DitroniX/IPEM-PiHat-IoT-Power-Energy-Monitor/Datasheets and Information/DitroniX.net Raspberry Pi 5 - Heatsink and Fan.jpg

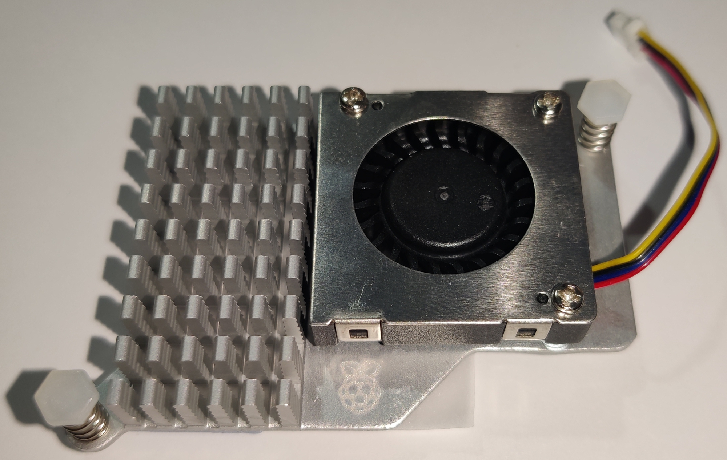
Datasheets and Information/DitroniX.net Raspberry Pi 5 - Heatsink and Fan.jpg
