DitroniX/IPEM-PiHat-IoT-Power-Energy-Monitor/Datasheets and Information/DitroniX.net Raspberry Pi 5 - IPEM Power Energy Monitor Border.jpg

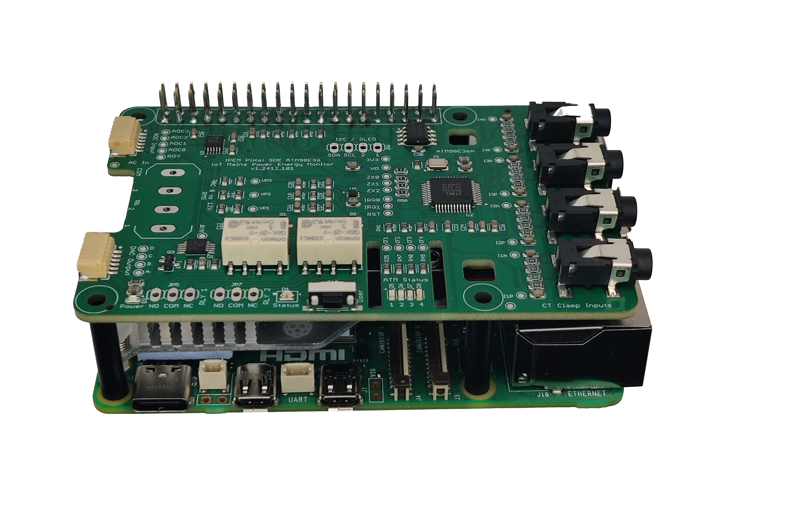
Datasheets and Information/DitroniX.net Raspberry Pi 5 - IPEM Power Energy Monitor Border.jpg
