DitroniX/IPEM-PiHat-IoT-Power-Energy-Monitor/Datasheets and Information/DitroniX.net Raspberry Pi 5 -Fan Socket.jpg

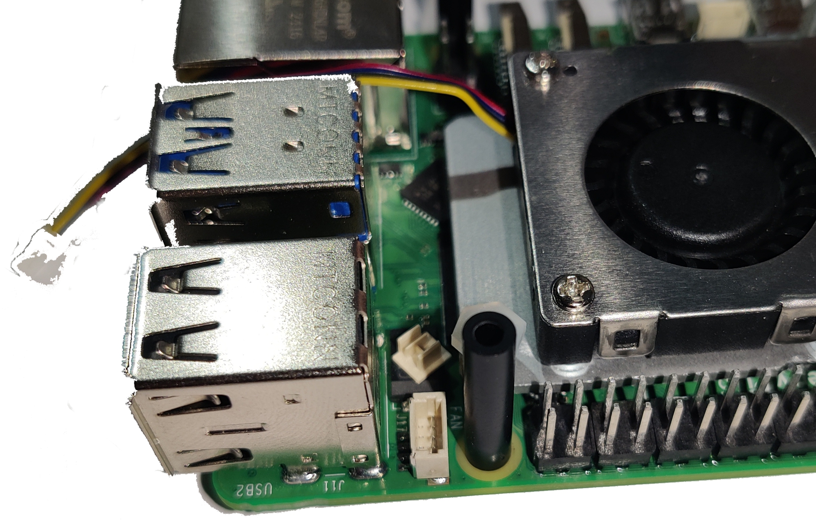
Datasheets and Information/DitroniX.net Raspberry Pi 5 -Fan Socket.jpg
