DitroniX/IPEM-PiHat-IoT-Power-Energy-Monitor/Datasheets and Information/IPEM PiHat 1.2502.102 PreProd BTM.jpg

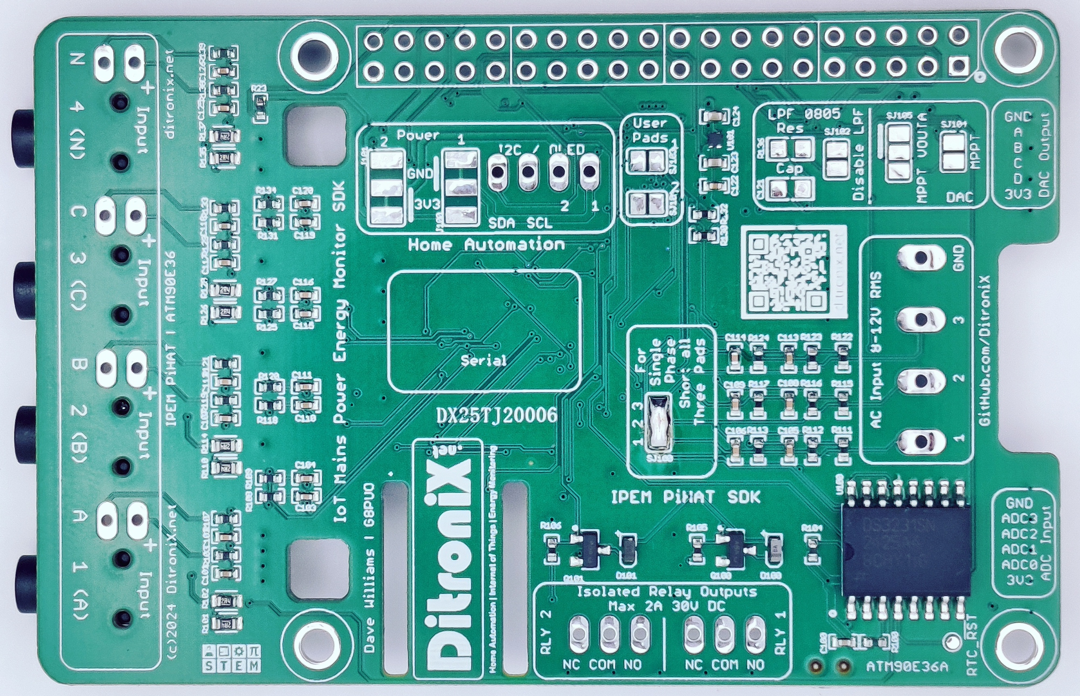
Datasheets and Information/IPEM PiHat 1.2502.102 PreProd BTM.jpg
