DitroniX/IPEM-PiHat-IoT-Power-Energy-Monitor/Datasheets and Information/IPEM PiHat - Single Phase Jumpers.png

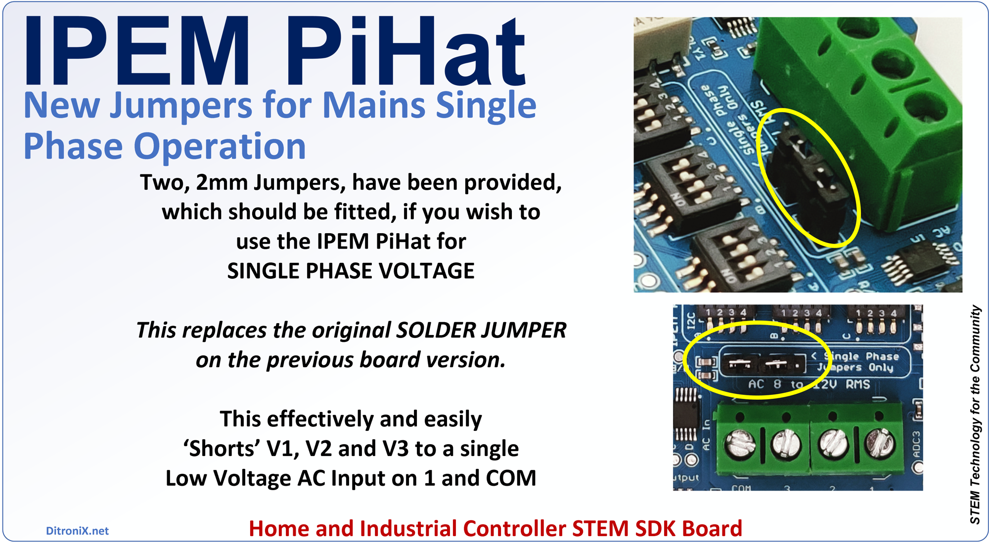
Datasheets and Information/IPEM PiHat - Single Phase Jumpers.png
