DitroniX/IPEM-PiHat-IoT-Power-Energy-Monitor/Datasheets and Information/IPEM PiHat Accessories.jpg

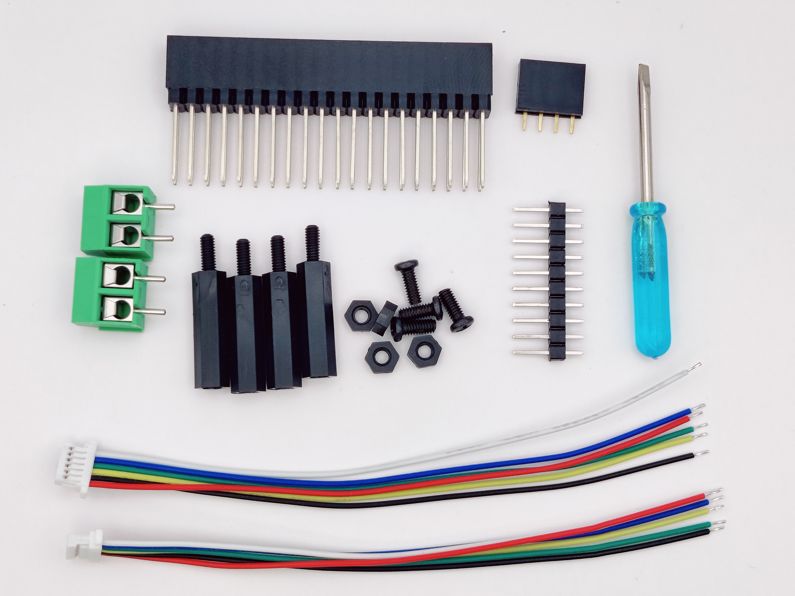
Datasheets and Information/IPEM PiHat Accessories.jpg
