DitroniX/IPEM-PiHat-IoT-Power-Energy-Monitor/Datasheets and Information/IPEM PiHat ATM90E32 ATM90E36 Beta Preview.png

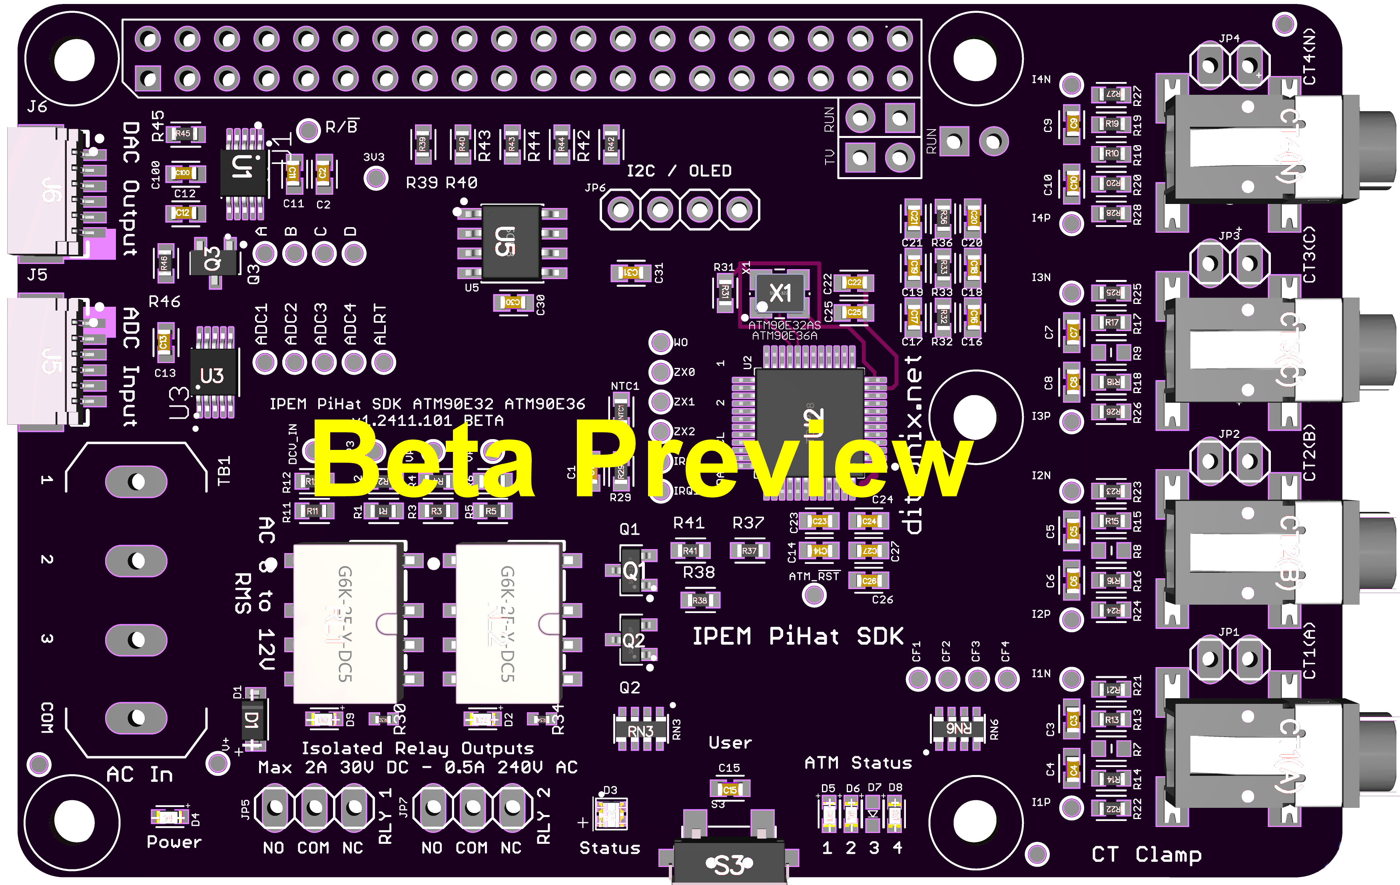
Datasheets and Information/IPEM PiHat ATM90E32 ATM90E36 Beta Preview.png
