DitroniX/IPEM-PiHat-IoT-Power-Energy-Monitor/Datasheets and Information/IPEM PiHat Comparison Chart.jpg

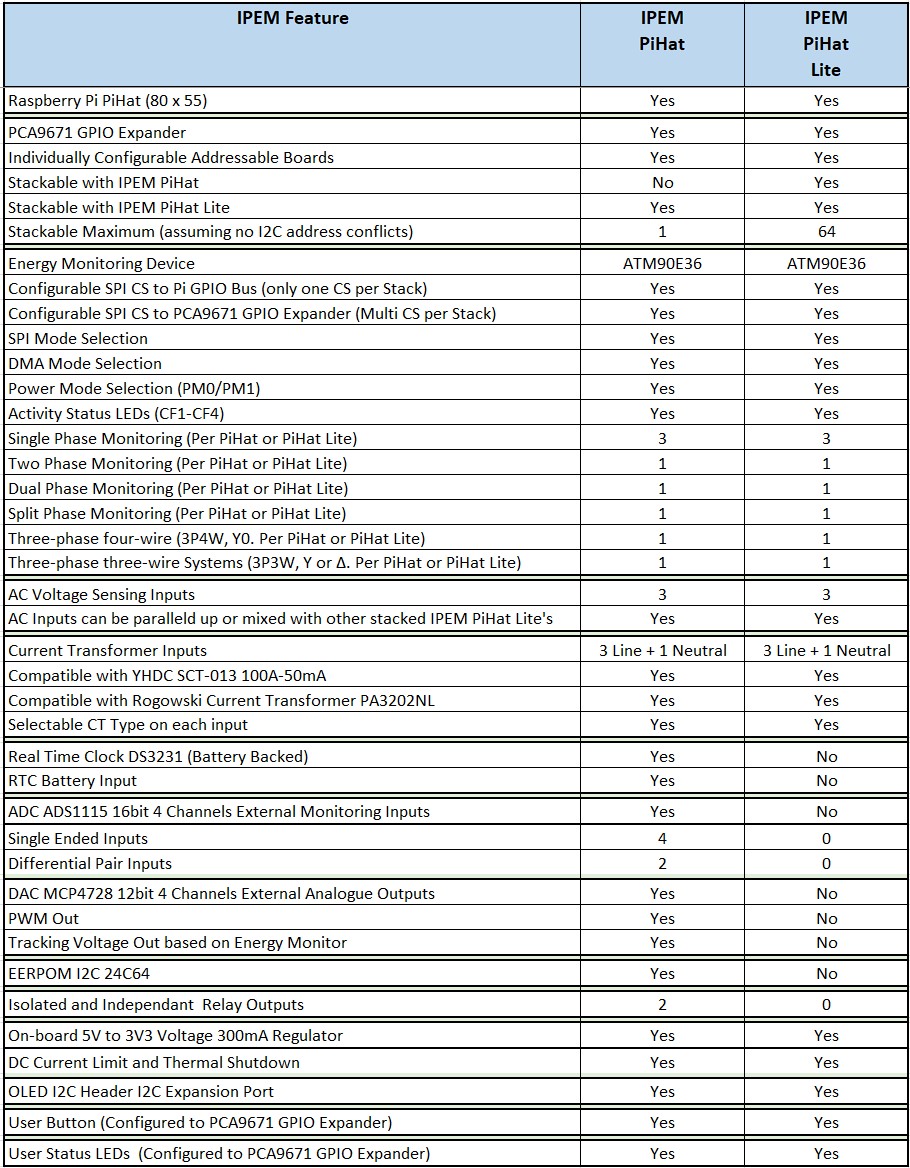
Datasheets and Information/IPEM PiHat Comparison Chart.jpg
