DitroniX/IPEM-PiHat-IoT-Power-Energy-Monitor/Datasheets and Information/IPEM PiHat Header GPIOs.jpg

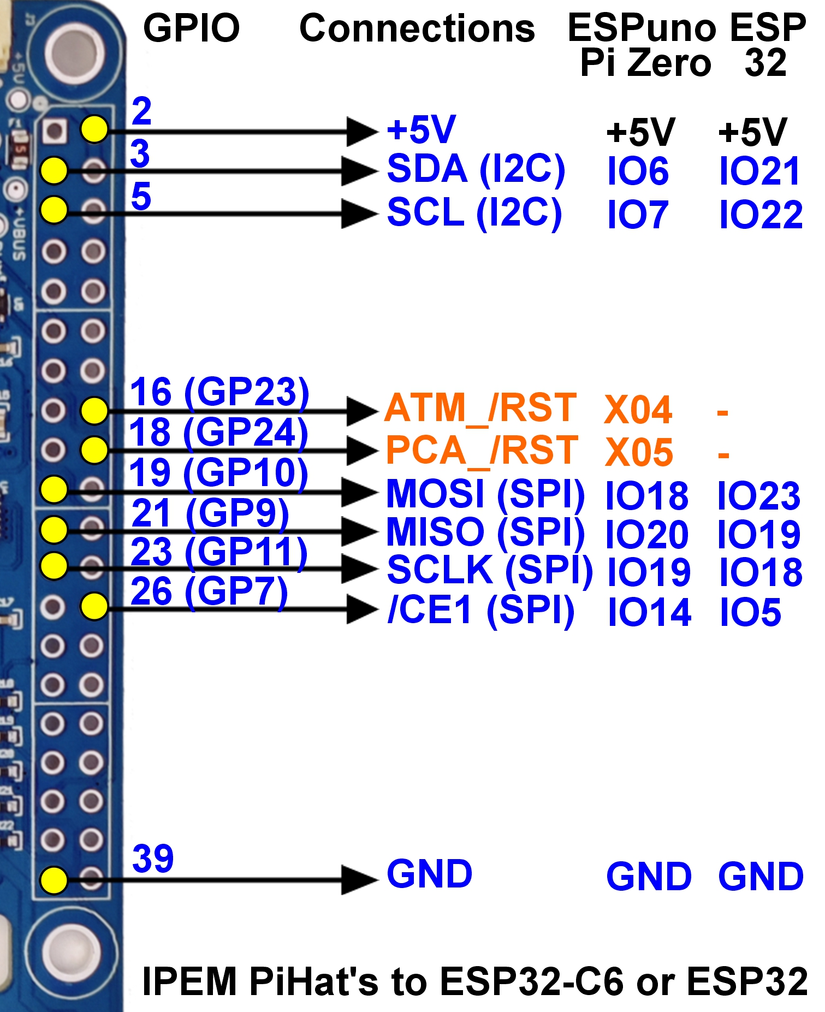
Datasheets and Information/IPEM PiHat Header GPIOs.jpg
