DitroniX/IPEM-PiHat-IoT-Power-Energy-Monitor/Datasheets and Information/IPEM PiHat Isolated Relays.jpg

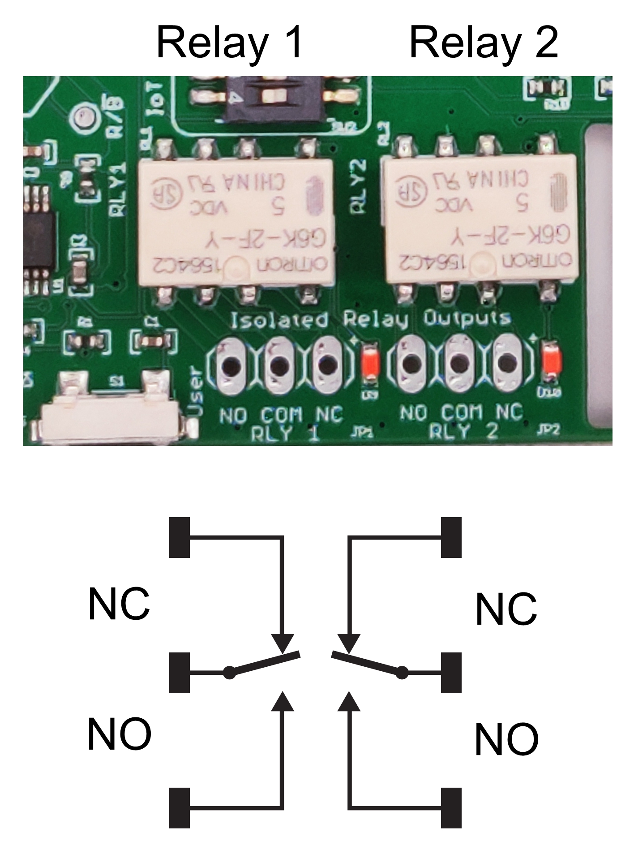
Datasheets and Information/IPEM PiHat Isolated Relays.jpg
