DitroniX/IPEM-PiHat-IoT-Power-Energy-Monitor/Datasheets and Information/IPEM PiHat Layout Topology - DIP Switches.jpg

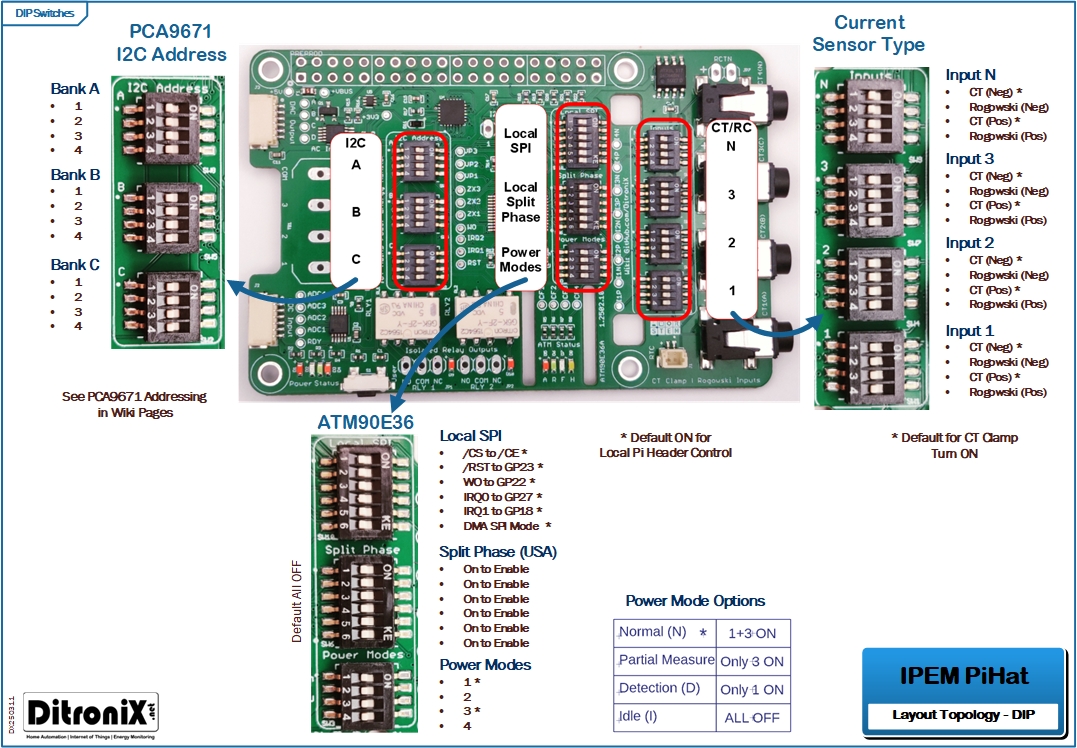
Datasheets and Information/IPEM PiHat Layout Topology - DIP Switches.jpg
