DitroniX/IPEM-PiHat-IoT-Power-Energy-Monitor/Datasheets and Information/IPEM PiHat Lite - Default I2C Scan.png

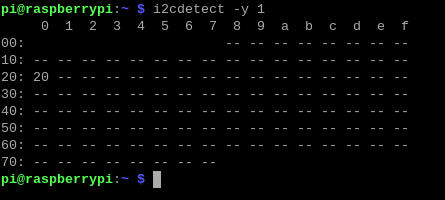
Datasheets and Information/IPEM PiHat Lite - Default I2C Scan.png
