DitroniX/IPEM-PiHat-IoT-Power-Energy-Monitor/Datasheets and Information/IPEM PiHat Lite Bottom.jpg

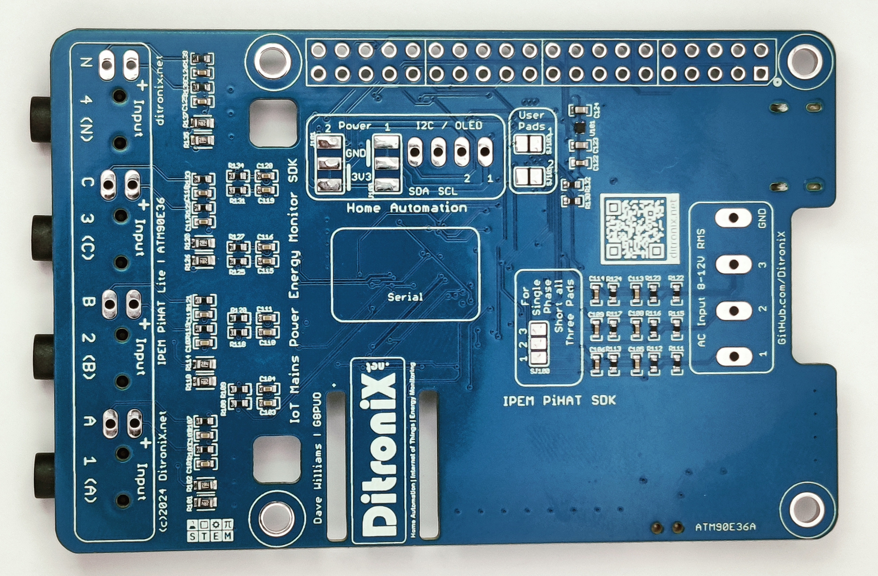
Datasheets and Information/IPEM PiHat Lite Bottom.jpg
