DitroniX/IPEM-PiHat-IoT-Power-Energy-Monitor/Datasheets and Information/IPEM PiHat Lite Layout Config Top.png

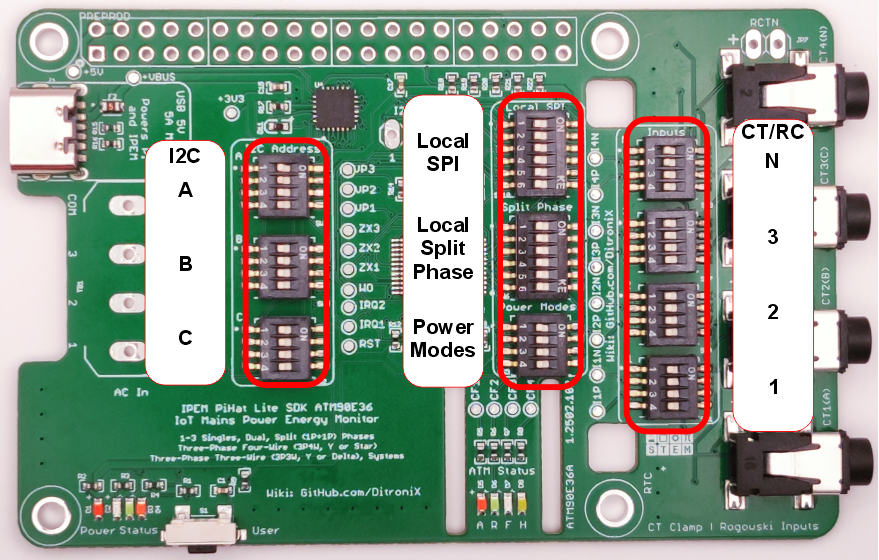
Datasheets and Information/IPEM PiHat Lite Layout Config Top.png
