DitroniX/IPEM-PiHat-IoT-Power-Energy-Monitor/Datasheets and Information/IPEM PiHat Lite Layout DIP Defaults for Local - Close Up.jpg

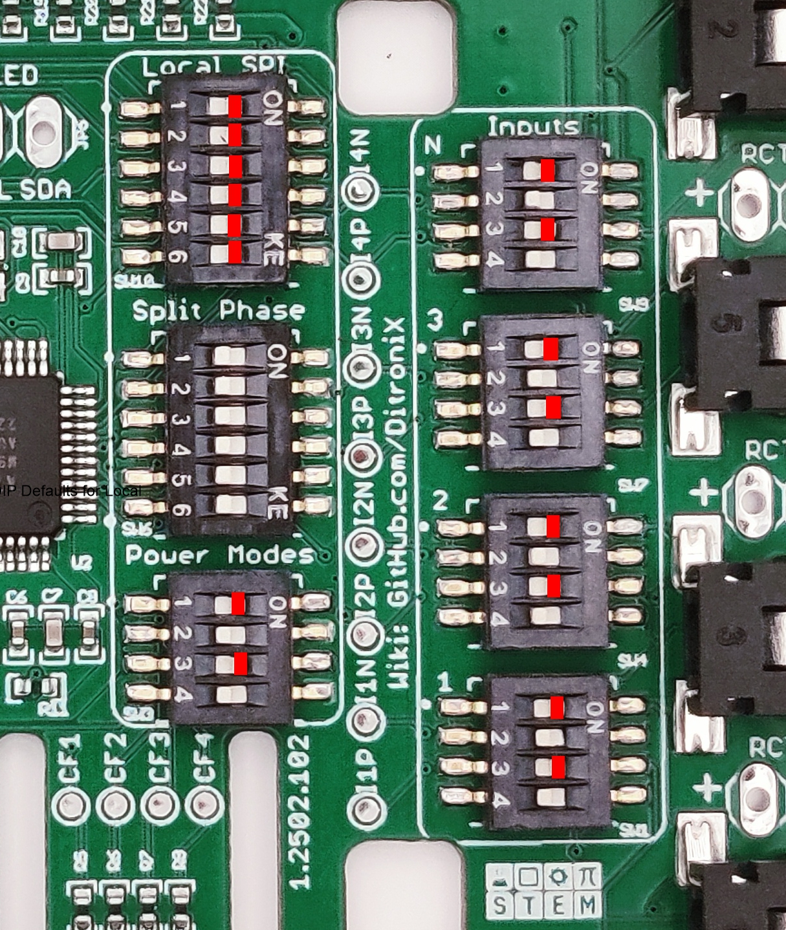
Datasheets and Information/IPEM PiHat Lite Layout DIP Defaults for Local - Close Up.jpg
