DitroniX/IPEM-PiHat-IoT-Power-Energy-Monitor/Datasheets and Information/IPEM PiHat Lite Layout Topology -  Devices Bottom.jpg

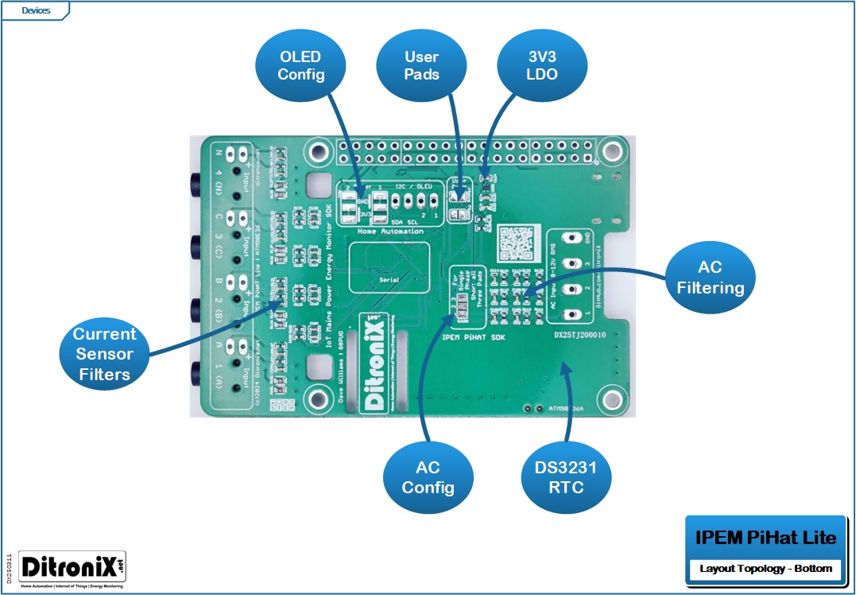
Datasheets and Information/IPEM PiHat Lite Layout Topology - Devices Bottom.jpg
