DitroniX/IPEM-PiHat-IoT-Power-Energy-Monitor/Datasheets and Information/IPEM PiHat Lite Layout Topology -  Devices Top.jpg

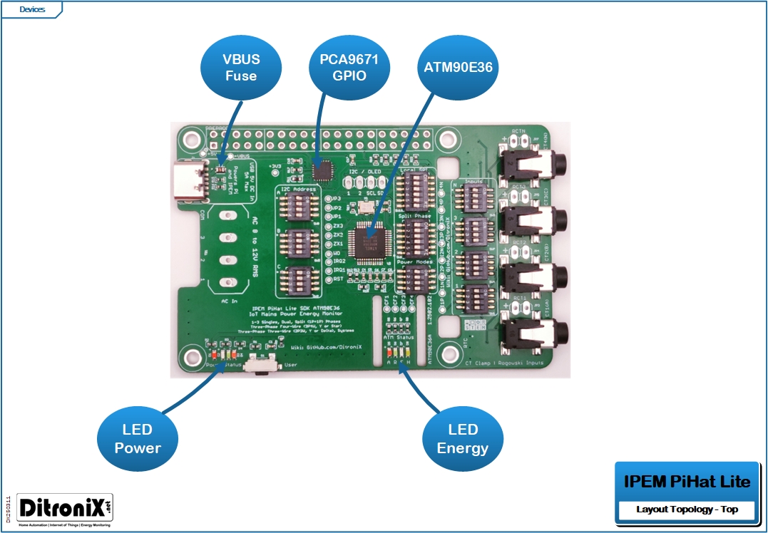
Datasheets and Information/IPEM PiHat Lite Layout Topology - Devices Top.jpg
