DitroniX/IPEM-PiHat-IoT-Power-Energy-Monitor/Datasheets and Information/IPEM PiHat Lite Layout Topology - Interfaces.jpg

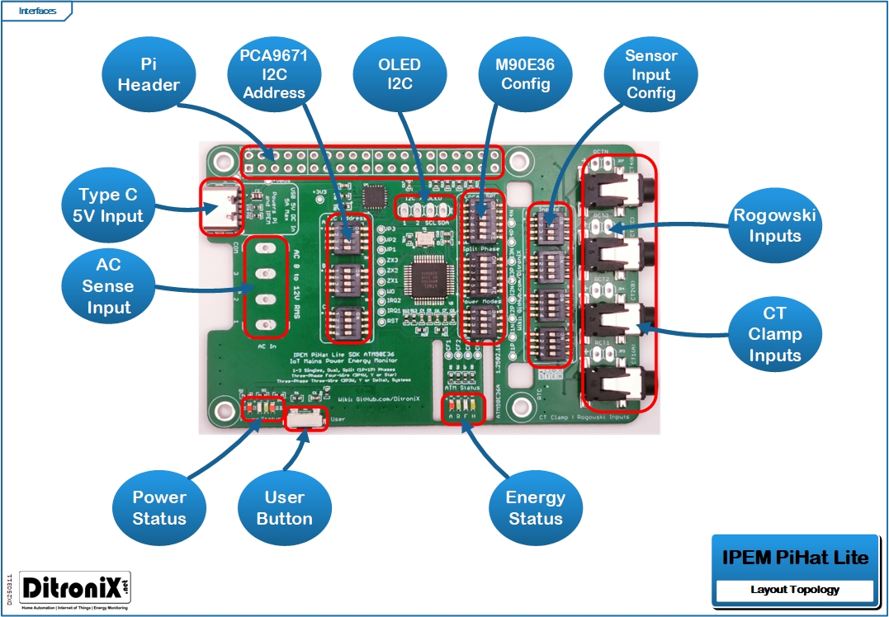
Datasheets and Information/IPEM PiHat Lite Layout Topology - Interfaces.jpg
