DitroniX/IPEM-PiHat-IoT-Power-Energy-Monitor/Datasheets and Information/IPEM PiHat Lite Topology.png

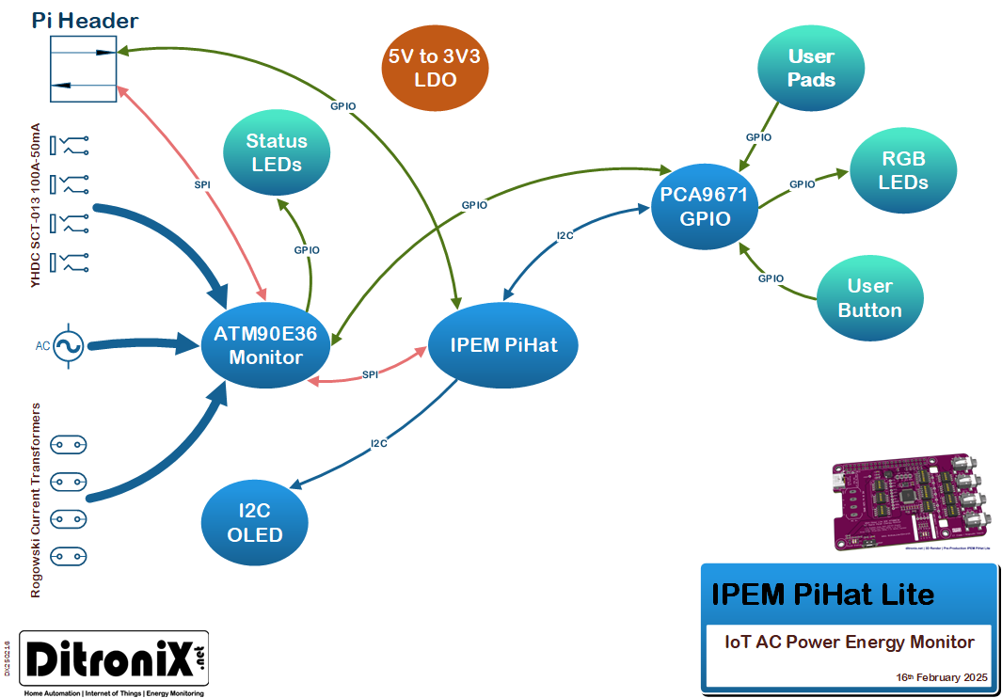
Datasheets and Information/IPEM PiHat Lite Topology.png
