DitroniX/IPEM-PiHat-IoT-Power-Energy-Monitor/Datasheets and Information/IPEM PiHat Packaged.jpg

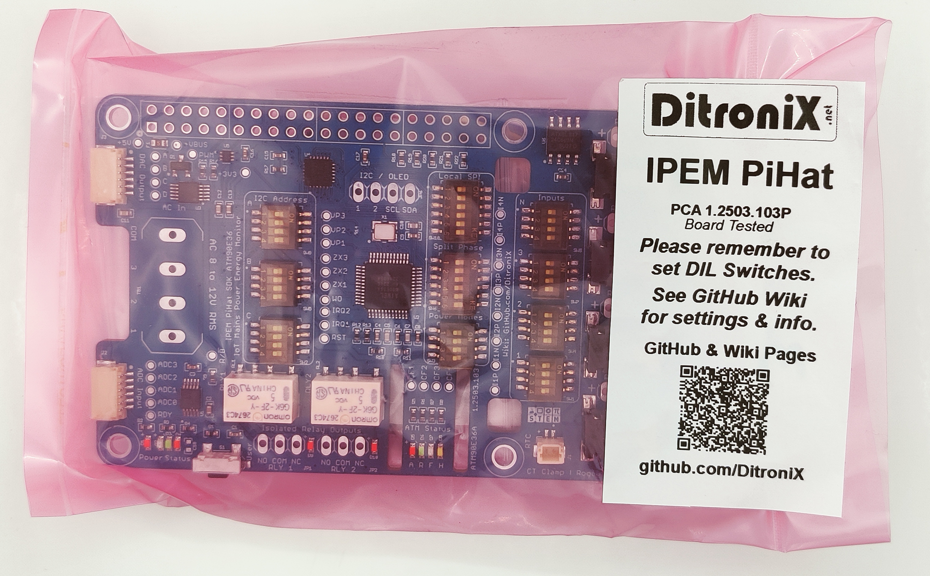
Datasheets and Information/IPEM PiHat Packaged.jpg
