DitroniX/IPEM-PiHat-IoT-Power-Energy-Monitor/Datasheets and Information/IPEM PiHat RTC Battery.jpg

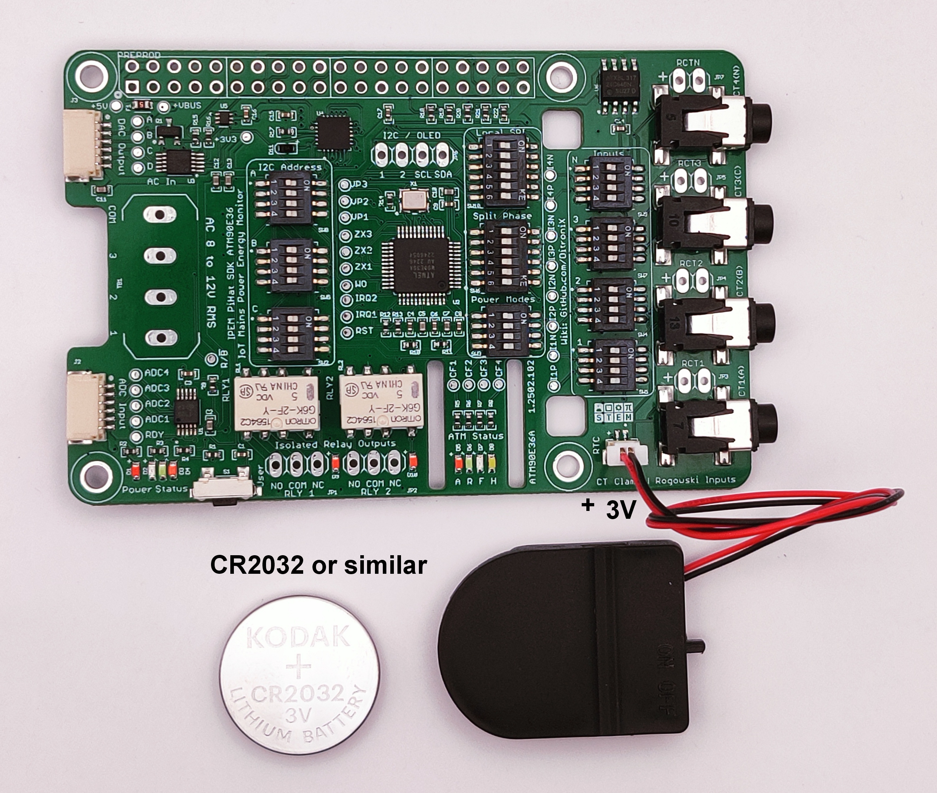
Datasheets and Information/IPEM PiHat RTC Battery.jpg
