DitroniX/IPEM-PiHat-IoT-Power-Energy-Monitor/Datasheets and Information/IPEM PiHat Stackable Enclosure DRAFT 1.jpg

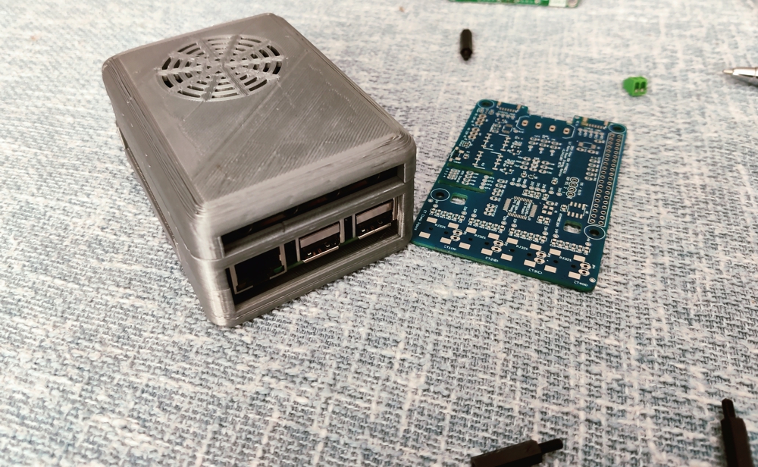
Datasheets and Information/IPEM PiHat Stackable Enclosure DRAFT 1.jpg
