DitroniX/IPEM-PiHat-IoT-Power-Energy-Monitor/Datasheets and Information/IPEM PiHat Stackable Enclosure DRAFT 3.jpg

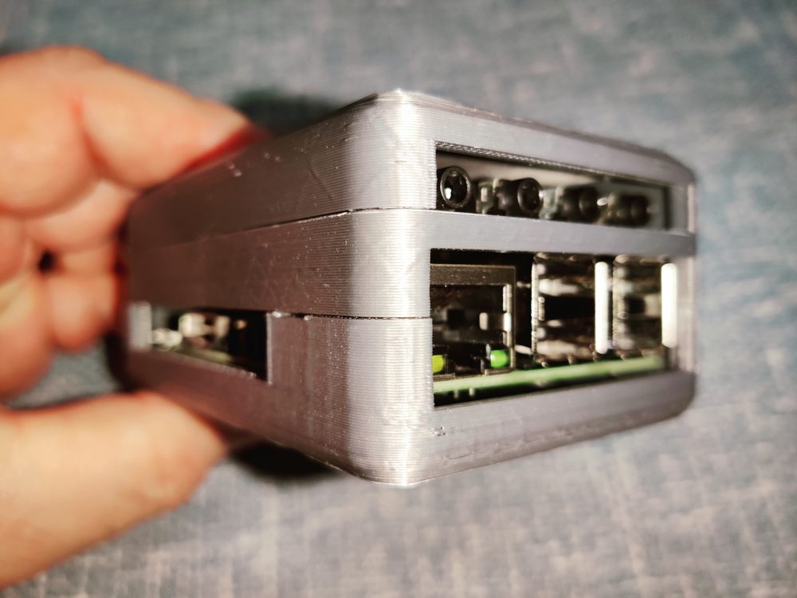
Datasheets and Information/IPEM PiHat Stackable Enclosure DRAFT 3.jpg
