DitroniX/IPEM-PiHat-IoT-Power-Energy-Monitor/Datasheets and Information/IPEM PiHat Stacking Examples.jpg

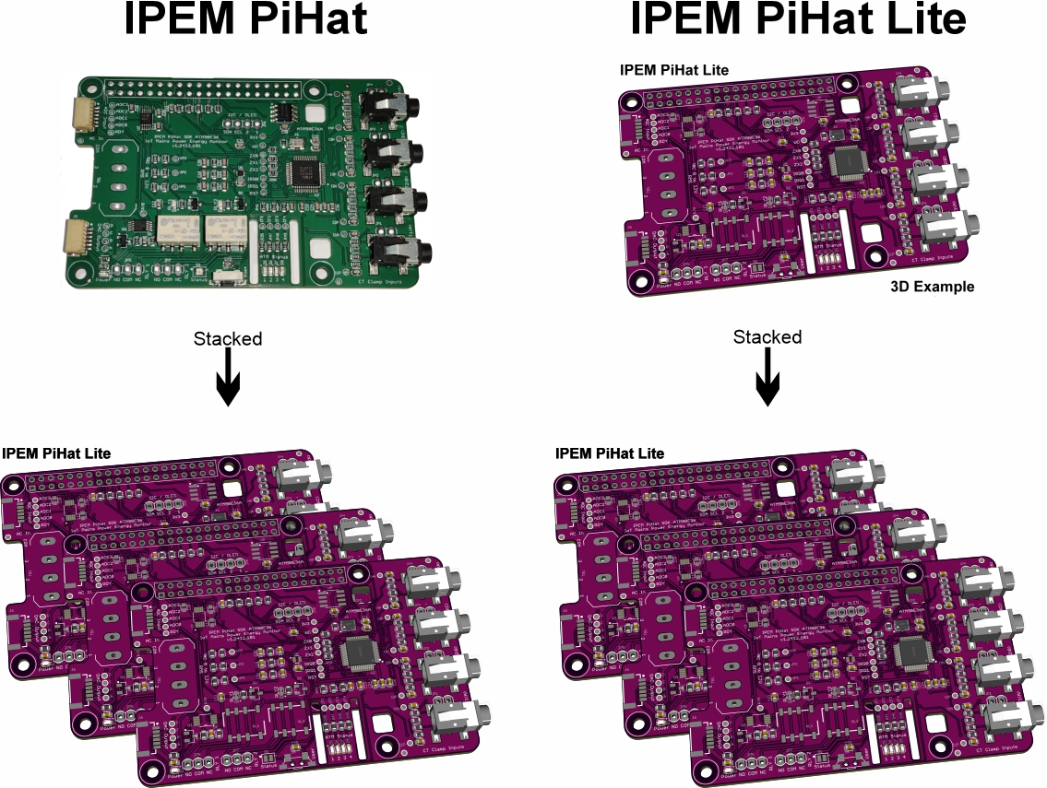
Datasheets and Information/IPEM PiHat Stacking Examples.jpg
