DitroniX/IPEM-PiHat-IoT-Power-Energy-Monitor/Datasheets and Information/IPEM PiHat Topology.png

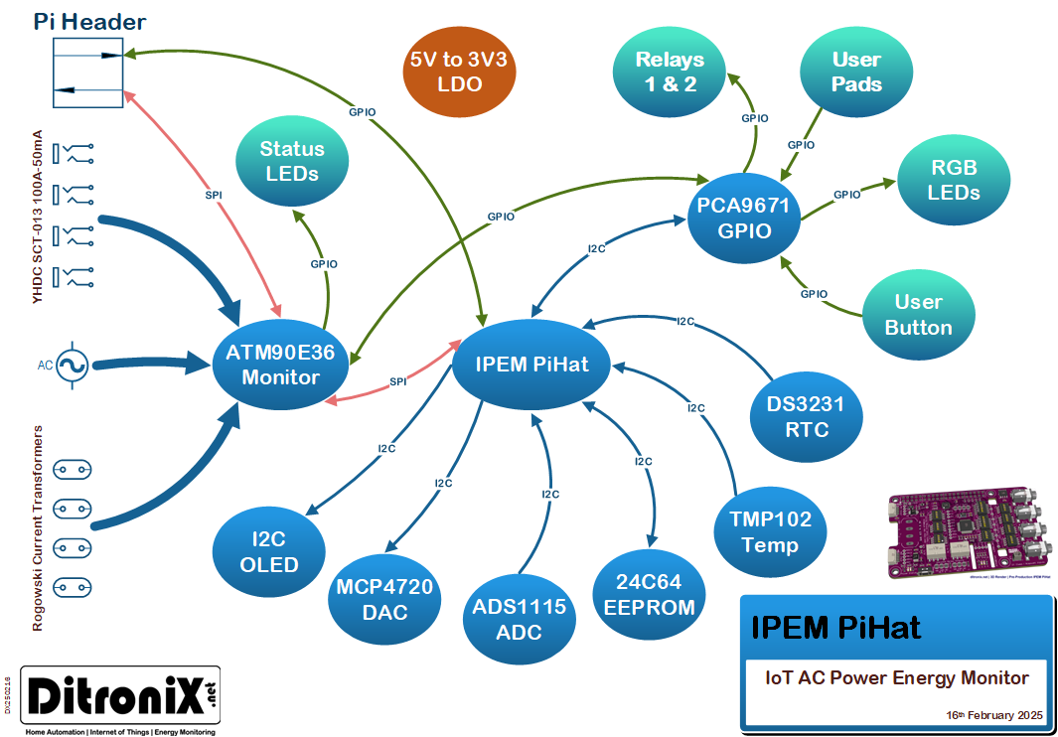
Datasheets and Information/IPEM PiHat Topology.png
