DitroniX/IPEM-PiHat-IoT-Power-Energy-Monitor/Datasheets and Information/IPEM PiHat with Display.jpg

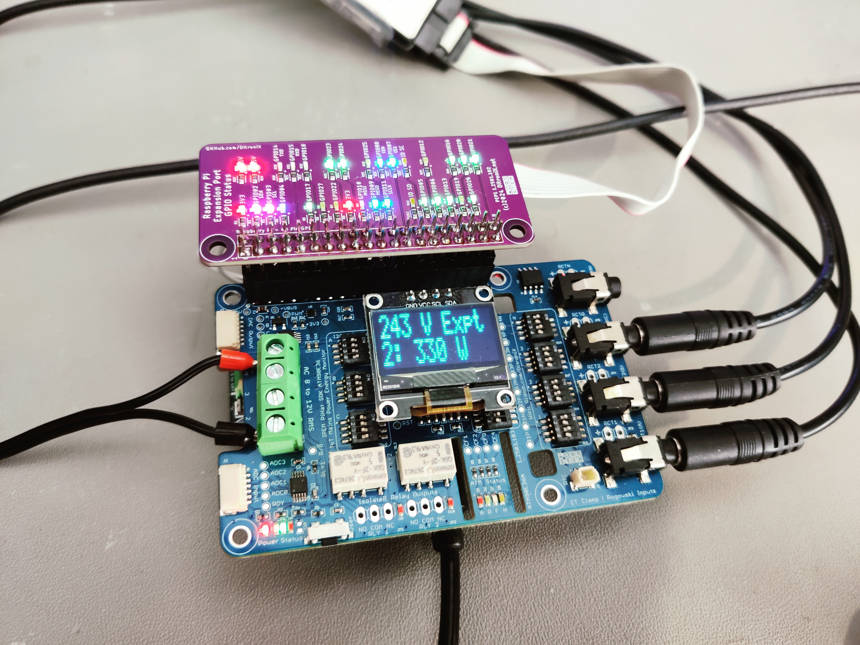
Datasheets and Information/IPEM PiHat with Display.jpg
