DitroniX/IPEM-PiHat-IoT-Power-Energy-Monitor/Datasheets and Information/IPEM PiHat with ESPuno Pi Zero.jpg

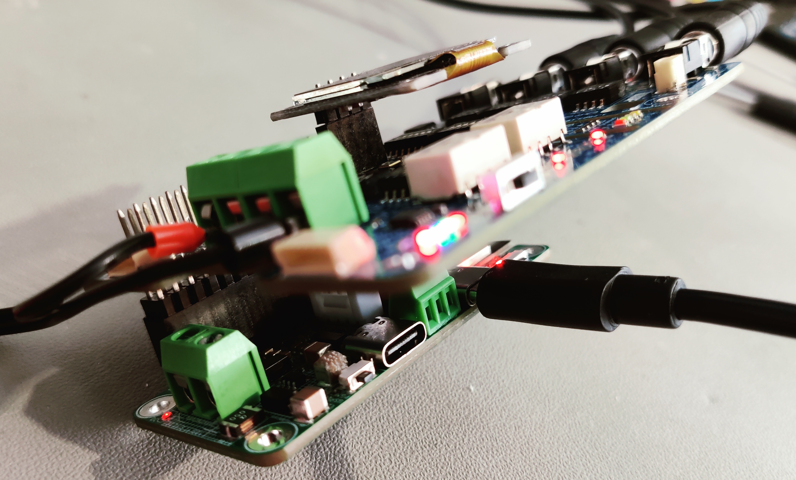
Datasheets and Information/IPEM PiHat with ESPuno Pi Zero.jpg
