DitroniX/IPEM-PiHat-IoT-Power-Energy-Monitor/Datasheets and Information/IPEM Raspberry Pi PiHat ATM90E36 Energy Monitor 1.2412.101 3D Bottom.png

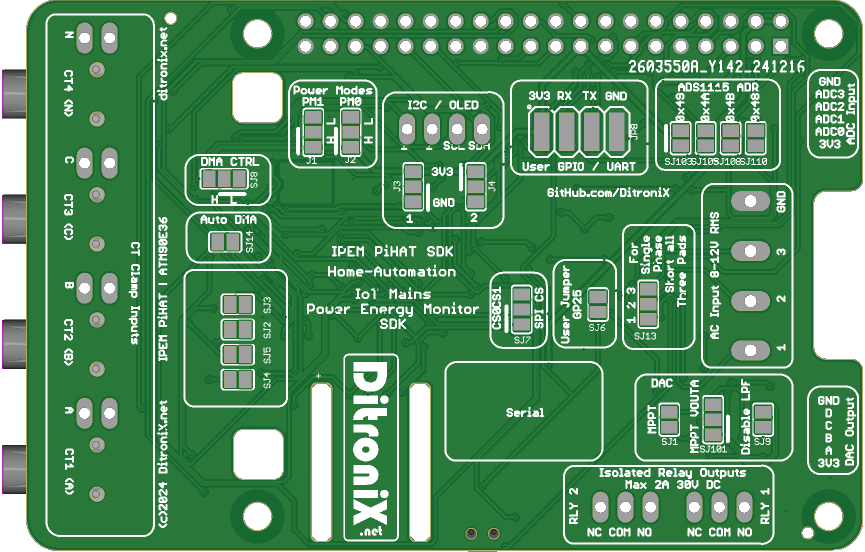
Datasheets and Information/IPEM Raspberry Pi PiHat ATM90E36 Energy Monitor 1.2412.101 3D Bottom.png
