DitroniX/IPEM-PiHat-IoT-Power-Energy-Monitor/Datasheets and Information/IPEM Raspberry Pi PiHat Lite ATM90E36 1.2501.101 Angled Top 3D.png

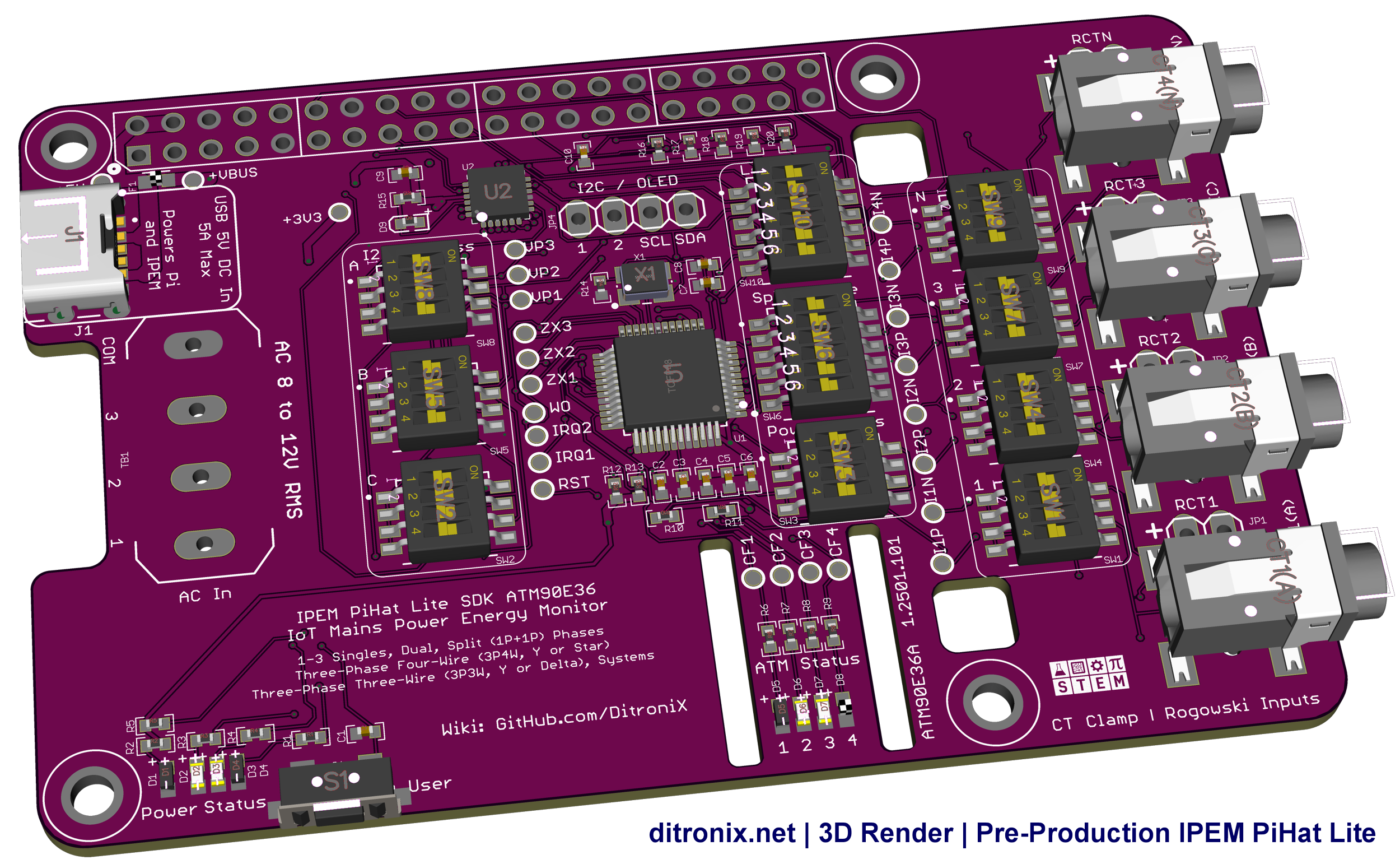
Datasheets and Information/IPEM Raspberry Pi PiHat Lite ATM90E36 1.2501.101 Angled Top 3D.png
