DitroniX/IPEM-PiHat-IoT-Power-Energy-Monitor/Datasheets and Information/IPEM Raspberry Pi PiHat Lite ATM90E36 1.2503.103 Schematic.png

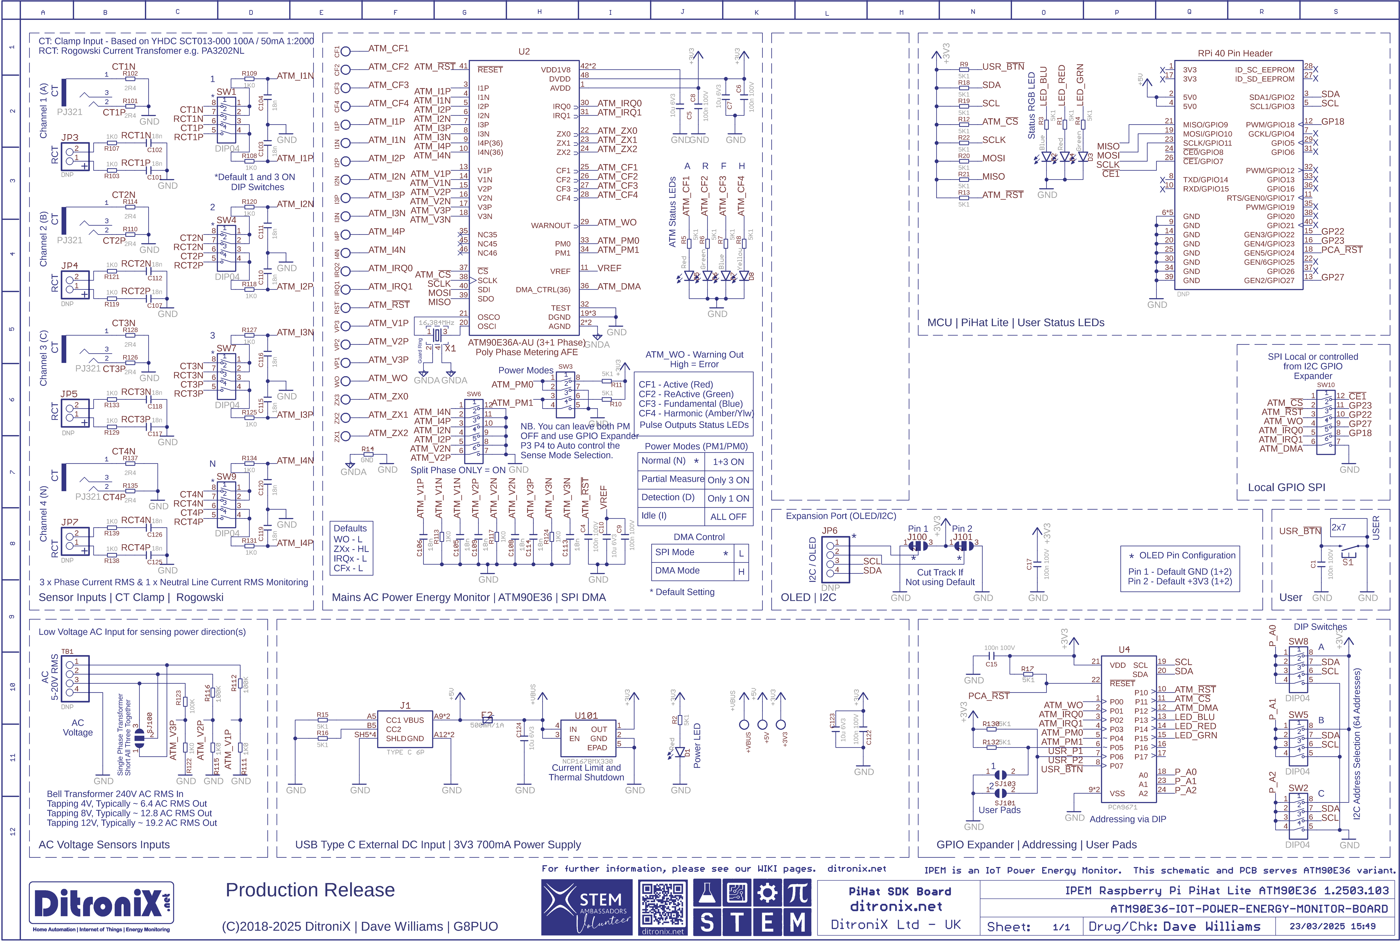
Datasheets and Information/IPEM Raspberry Pi PiHat Lite ATM90E36 1.2503.103 Schematic.png
