DitroniX/IPEM-PiHat-IoT-Power-Energy-Monitor/Datasheets and Information/PCA9671 GPIO Expander Defaults.jpg

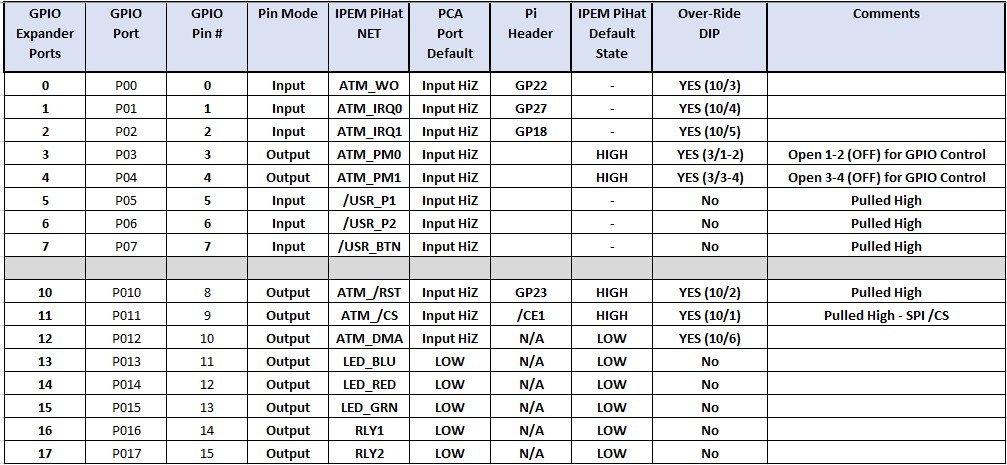
Datasheets and Information/PCA9671 GPIO Expander Defaults.jpg
