DitroniX/IPEM-PiHat-IoT-Power-Energy-Monitor/Datasheets and Information/IPEM Raspberry Pi PiHat Lite ATM90E36 1.2501.101 PCB Components Btm.png

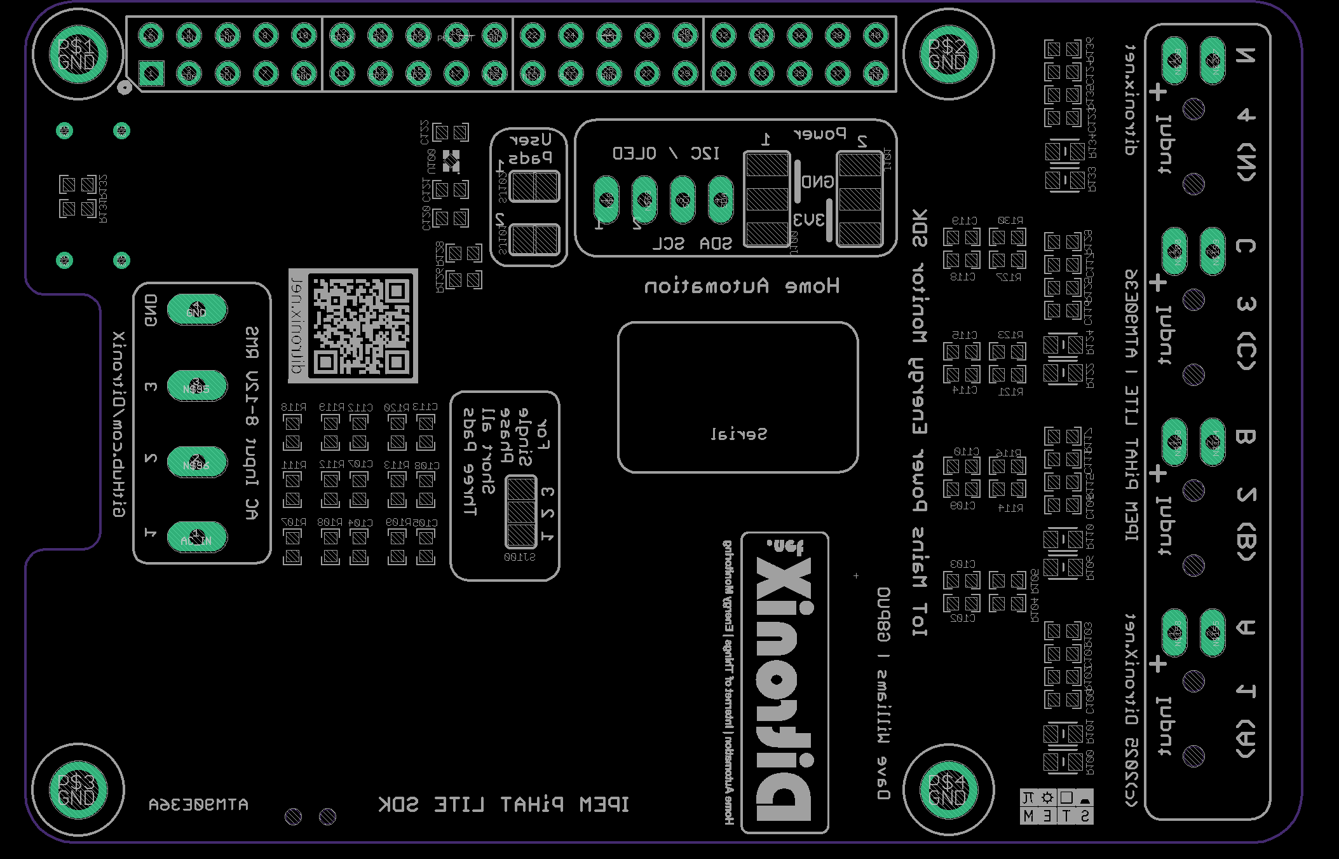
Datasheets and Information/IPEM Raspberry Pi PiHat Lite ATM90E36 1.2501.101 PCB Components Btm.png
