DitroniX/IPEM-PiHat-IoT-Power-Energy-Monitor/Datasheets and Information/IPEM PiHat Stacked - Testing.JPG

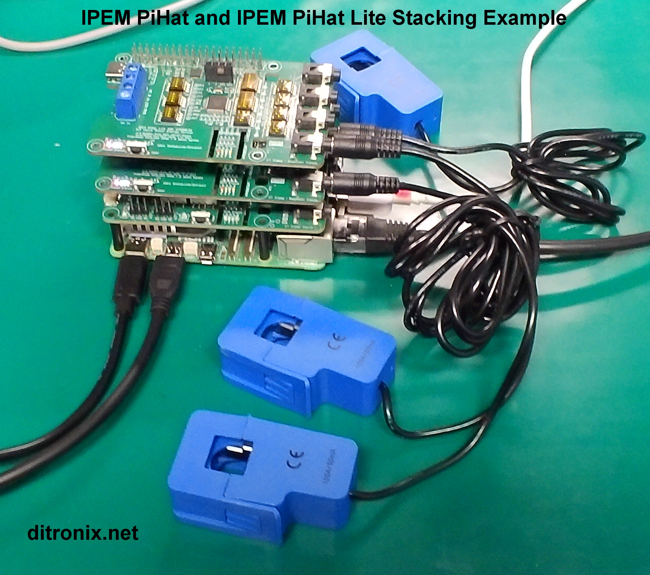
Datasheets and Information/IPEM PiHat Stacked - Testing.JPG
